zwenergy/picoDuck/code/multiROM/rom_menu.h

unsigned char rom[ 131072 ] = {
0xc3, 0x50, 0x01, 0xff, 0xff, 0xff, 0xff, 0xff, 0xff, 0xff, 0xff, 0xff
, 0xff, 0xff, 0xff, 0xff, 0xff, 0xff, 0xff, 0xff, 0xff, 0xff, 0xff, 0xff
, 0xff, 0xff, 0xff, 0xff, 0xff, 0xff, 0xff, 0xff, 0xe9, 0xff, 0xff, 0xff
, 0xff, 0xff, 0xff, 0xff, 0x22, 0x0d, 0x20, 0xfc, 0xc9, 0xff, 0xff, 0xff
, 0x1a, 0x22, 0x13, 0x0d, 0x20, 0xfa, 0xc9, 0xff, 0xff, 0xff, 0xff, 0xff
, 0xff, 0xff, 0xff, 0xff, 0xf5, 0xe5, 0x21, 0xa5, 0xc0, 0xc3, 0x80, 0x00
, 0xc3, 0xa1, 0x0e, 0xff, 0xff, 0xff, 0xff, 0xff, 0xff, 0xff, 0xff, 0xff
, 0xff, 0xff, 0xff, 0xff, 0xff, 0xff, 0xff, 0xff, 0xff, 0xff, 0xff, 0xff
, 0xff, 0xff, 0xff, 0xff, 0xff, 0xff, 0xff, 0xff, 0xff, 0xff, 0xff, 0xff
, 0xff, 0xff, 0xff, 0xff, 0xff, 0xff, 0xff, 0xff, 0xff, 0xff, 0xff, 0xff
, 0xff, 0xff, 0xff, 0xff, 0xff, 0xff, 0xff, 0xff, 0xc5, 0xd5, 0x2a, 0xb6
, 0x28, 0x0b, 0xe5, 0x3a, 0x6e, 0x67, 0xe7, 0xe1, 0x23, 0x18, 0xf3, 0xe8
, 0x04, 0xd1, 0xc1, 0xe1, 0xf0, 0x11, 0xe6, 0x02, 0x20, 0xfa, 0xf1, 0xd9
, 0x21, 0xa3, 0xc0, 0x34, 0x20, 0x02, 0x23, 0x34, 0x3e, 0x01, 0xe0, 0x91
, 0xc3, 0x80, 0xff, 0xf0, 0x11, 0xe6, 0x02, 0x20, 0xfa, 0x3e, 0xc0, 0xc3
, 0x84, 0xff, 0xaf, 0x01, 0x2f, 0x00, 0x21, 0xa0, 0xc0, 0xcd, 0xe2, 0x07
, 0x3e, 0xc0, 0xe0, 0x92, 0x67, 0xaf, 0x6f, 0x0e, 0xa0, 0xc3, 0x28, 0x00
, 0xf3, 0xe0, 0xff, 0xaf, 0xfb, 0xe0, 0x0f, 0xc9, 0xf0, 0x92, 0xb7, 0xc8
, 0xe0, 0x1a, 0x3e, 0x28, 0x3d, 0x20, 0xfd, 0xc9, 0xff, 0xff, 0xff, 0xff
, 0xff, 0xff, 0xff, 0xff, 0xff, 0xff, 0xff, 0xff, 0xff, 0xff, 0xff, 0xff
, 0xc9, 0xff, 0xff, 0xff, 0xff, 0xff, 0xff, 0xff, 0xc3, 0x4b, 0x0a, 0xff
, 0xff, 0xff, 0xff, 0xff, 0xff, 0xff, 0xff, 0xff, 0xff, 0xff, 0xff, 0xff
, 0xff, 0xff, 0xff, 0xff, 0xff, 0xff, 0xff, 0xff, 0xff, 0xff, 0xff, 0xff
, 0xff, 0xff, 0xff, 0xff, 0xff, 0xff, 0xff, 0xff, 0xff, 0xff, 0xff, 0xff
, 0xff, 0xff, 0xff, 0xff, 0xff, 0xff, 0xff, 0xff, 0xff, 0xff, 0xff, 0xff
, 0xff, 0xff, 0xff, 0xff, 0xff, 0xff, 0xff, 0xff, 0x00, 0x00, 0x00, 0x00
, 0x00, 0x00, 0x00, 0x00, 0x00, 0x00, 0x00, 0x00, 0x00, 0x00, 0x00, 0x00
, 0x30, 0x30, 0xff, 0x1b, 0x00, 0x00, 0x00, 0x33, 0xff, 0x3b, 0xb5, 0x47
, 0xf3, 0x31, 0x00, 0xe0, 0xd5, 0xcd, 0x08, 0x08, 0xcd, 0xb6, 0x00, 0xd1
, 0x3e, 0x01, 0xea, 0xa0, 0xc0, 0xaf, 0xea, 0xa1, 0xc0, 0xaf, 0xe0, 0x12
, 0xe0, 0x13, 0xe0, 0x11, 0xe0, 0x16, 0x3e, 0x07, 0xe0, 0x17, 0x11, 0xd4
, 0x00, 0x21, 0x80, 0xff, 0x0e, 0x0c, 0xf7, 0xcd, 0x80, 0xff, 0x11, 0x9c
, 0x00, 0xcd, 0xde, 0x01, 0x3e, 0xe4, 0xe0, 0x1b, 0xe0, 0x14, 0x3e, 0x1b
, 0xe0, 0x15, 0x3e, 0x88, 0xe0, 0x10, 0x3e, 0x01, 0xe0, 0xff, 0xaf, 0xe0
, 0x0f, 0x21, 0xa3, 0xc0, 0x22, 0x77, 0xe0, 0x45, 0x3c, 0xe0, 0x90, 0xcd
, 0x94, 0x10, 0xfb, 0xcd, 0x59, 0x02, 0x76, 0x00, 0x18, 0xfc, 0xf0, 0x10
, 0xe6, 0x80, 0xc8, 0xaf, 0xe0, 0x91, 0x76, 0x00, 0xf0, 0x91, 0xb7, 0x28
, 0xf9, 0xc9, 0x21, 0xa5, 0xc0, 0x2a, 0x4f, 0x2a, 0x47, 0xb1, 0xc8, 0x7b
, 0xb9, 0x20, 0xf6, 0x7a, 0xb8, 0x20, 0xf2, 0x44, 0x4d, 0x0b, 0x0b, 0x2a
, 0x02, 0x03, 0x57, 0x2a, 0x02, 0x03, 0xb2, 0x20, 0xf6, 0xc9, 0x21, 0xa5
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
};
